jvswise/DMXW/Documentation/DMX Wireless Network Documents/Diagrams/Screenshots/Screenshot--dev-ttyUSB0 - PuTTY-2.png

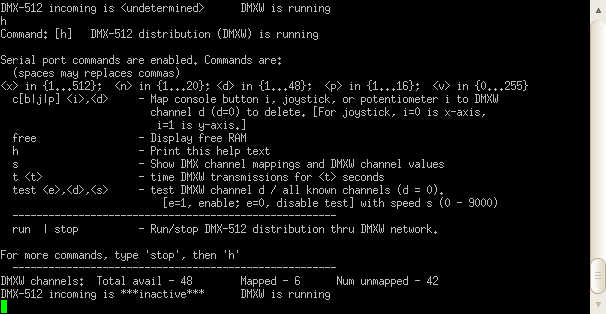
Documentation/DMX Wireless Network Documents/Diagrams/Screenshots/Screenshot--dev-ttyUSB0 - PuTTY-2.png
