jvswise/DMXW/Documentation/DMX Wireless Network Documents/Diagrams/Screenshots/Screenshot--dev-ttyUSB0 - PuTTY-3.png

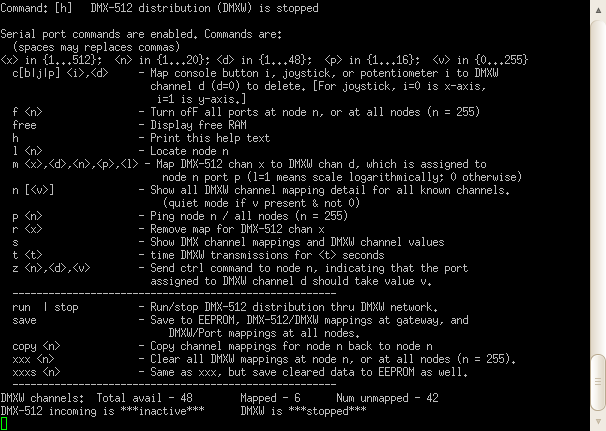
Documentation/DMX Wireless Network Documents/Diagrams/Screenshots/Screenshot--dev-ttyUSB0 - PuTTY-3.png
