jvswise/DMXW/Documentation/DMX Wireless Network Documents/Diagrams/Source Diagrams.bmp

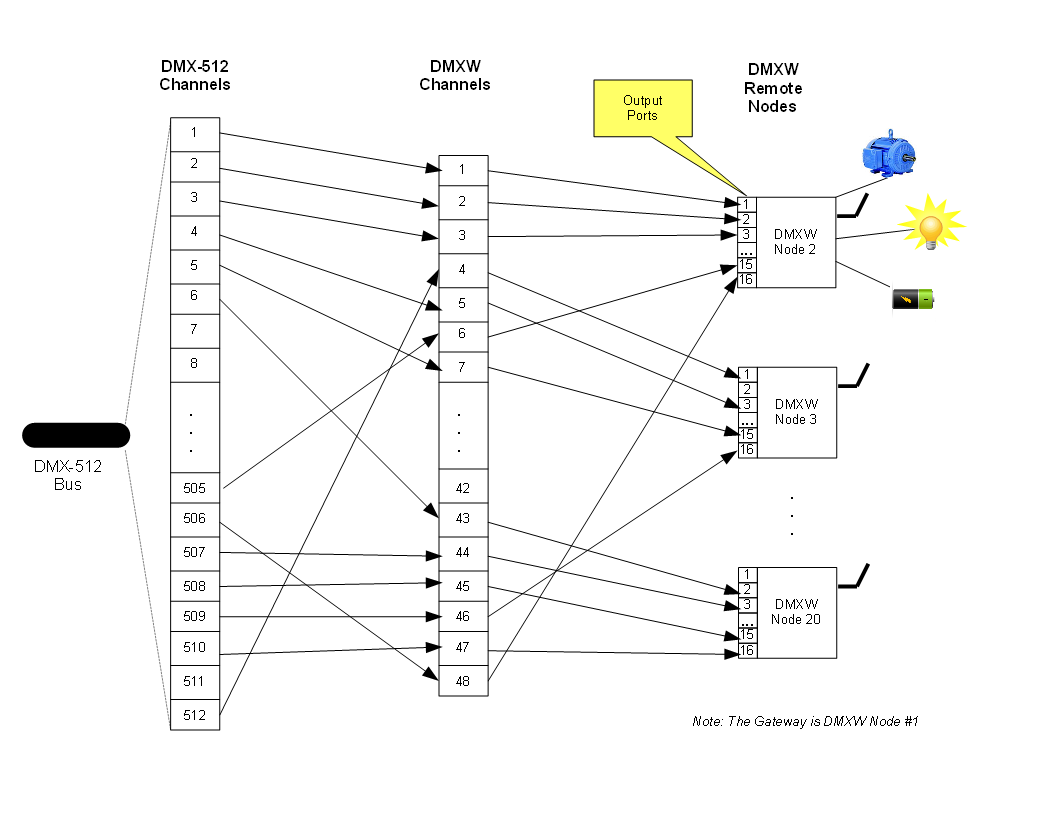
Documentation/DMX Wireless Network Documents/Diagrams/Source Diagrams.bmp
