jvswise/DMXW/Documentation/DMX Wireless Network Documents/FX modules info/Micro Fogger/DMXW micro fogger 2.jpg

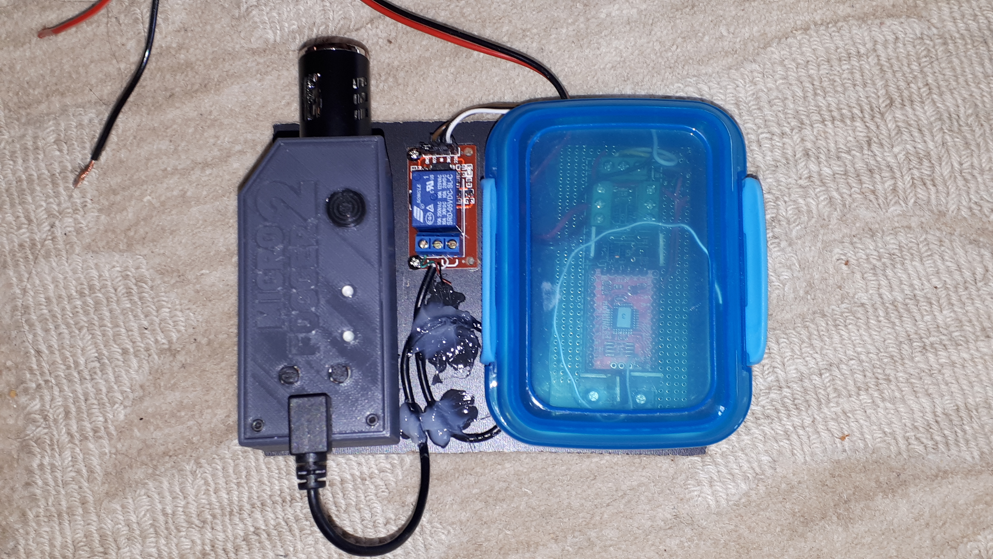
Documentation/DMX Wireless Network Documents/FX modules info/Micro Fogger/DMXW micro fogger 2.jpg
