jvswise/DMXW/Documentation/DMXW Tester Documents/DMXW Tester design notes.jpg

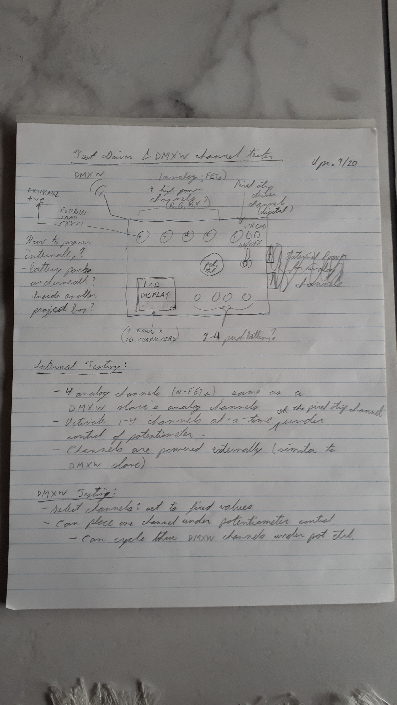
Documentation/DMXW Tester Documents/DMXW Tester design notes.jpg
