jvswise/DMXW/Documentation/DMXW Tester Documents/Photos/Channel 5 connections.jpg

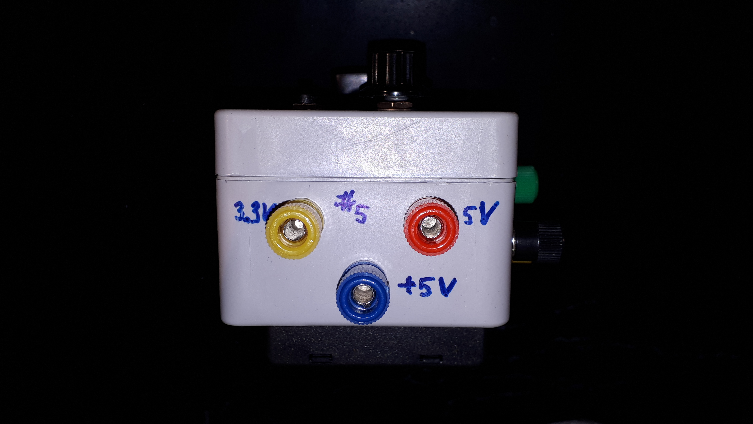
Documentation/DMXW Tester Documents/Photos/Channel 5 connections.jpg
