jvswise/DMXW/Documentation/DMXW Tester Documents/Photos/Display - Channels.jpg

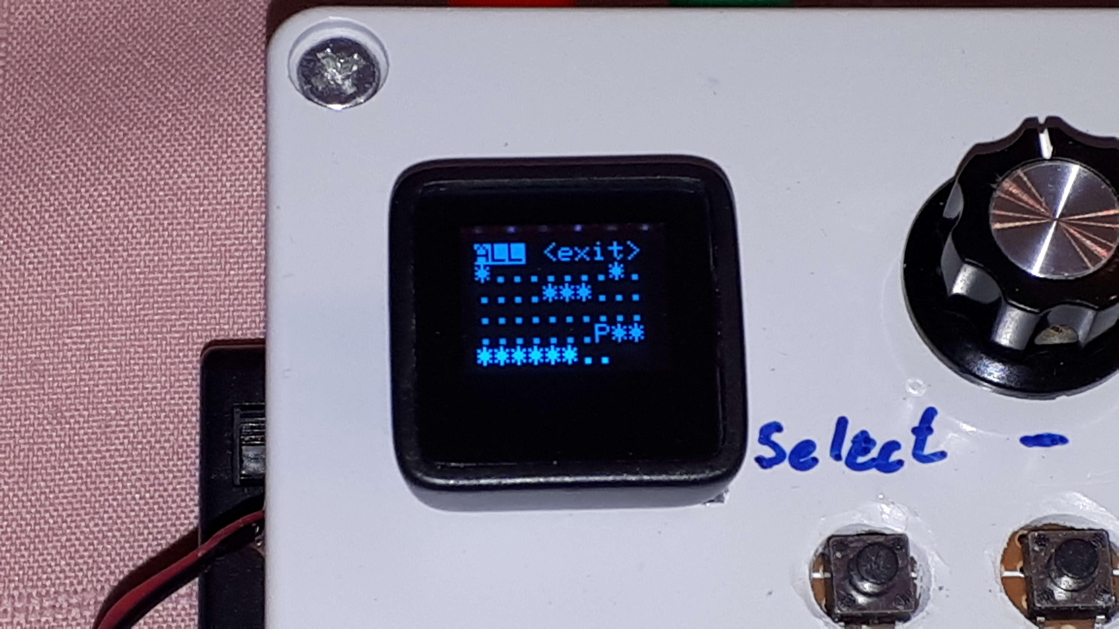
Documentation/DMXW Tester Documents/Photos/Display - Channels.jpg
