jvswise/DMXW/Documentation/DMXW Tester Documents/Photos/Display - params saved.jpg

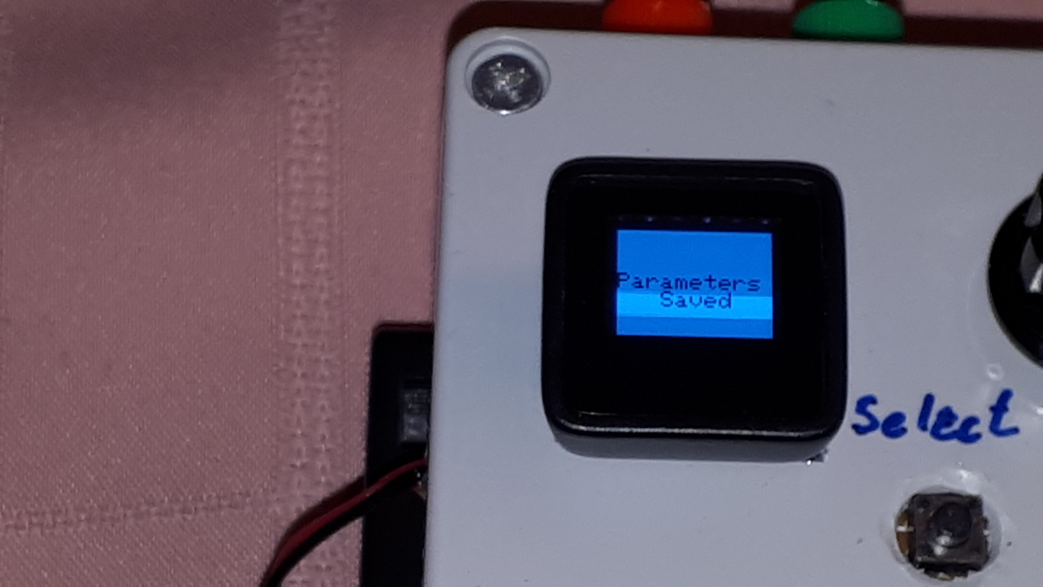
Documentation/DMXW Tester Documents/Photos/Display - params saved.jpg
