jvswise/DMXW/Documentation/DMXW Tester Documents/Photos/Display - test state.jpg

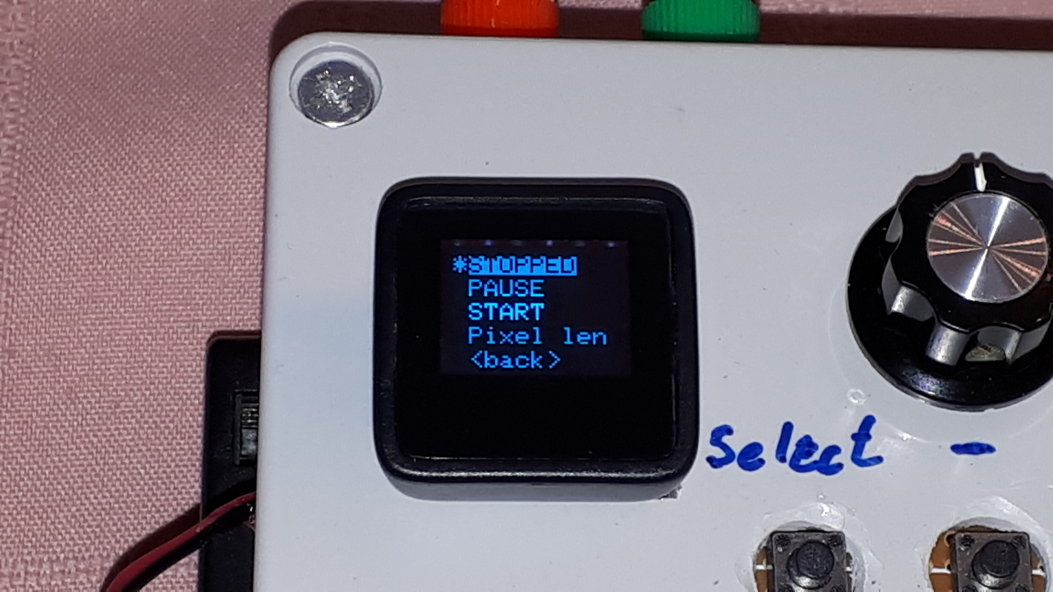
Documentation/DMXW Tester Documents/Photos/Display - test state.jpg
