jvswise/DMXW/Documentation/DMXW Tester Documents/Photos/Display - top level menu.jpg

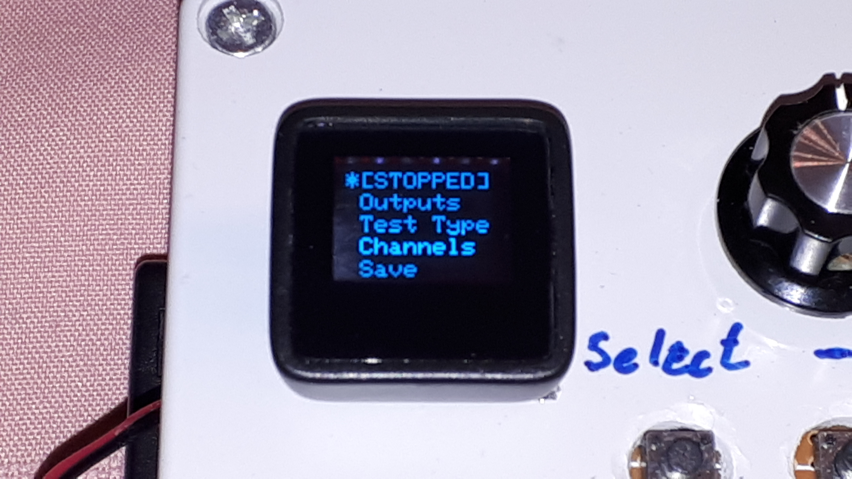
Documentation/DMXW Tester Documents/Photos/Display - top level menu.jpg
