jvswise/DMXW/Documentation/DMXW Tester Documents/Photos/Display - Values... .jpg

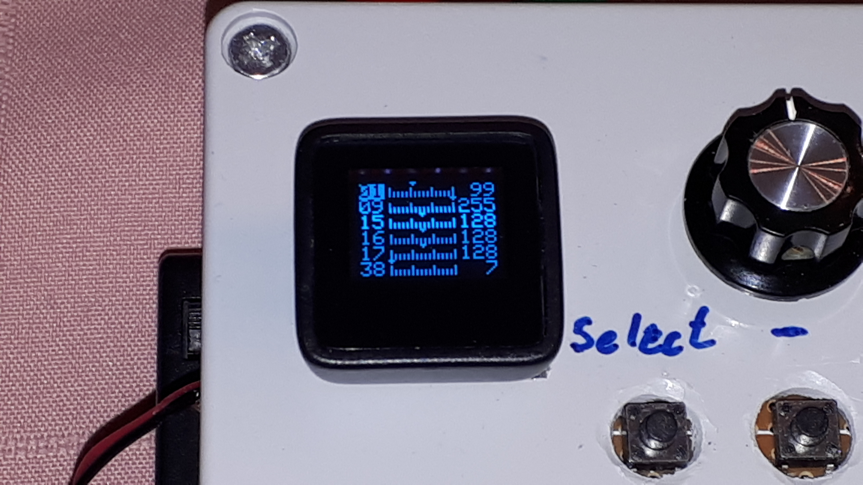
Documentation/DMXW Tester Documents/Photos/Display - Values... .jpg
