jvswise/DMXW/Documentation/DMXW Tester Documents/Photos/Top panel (battery pack underneath).jpg

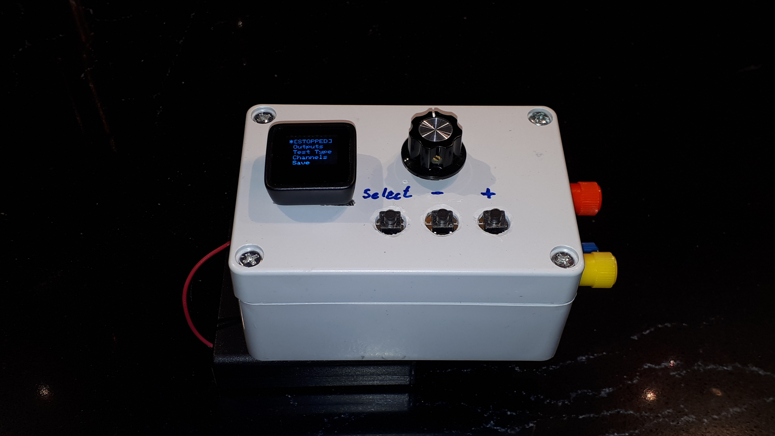
Documentation/DMXW Tester Documents/Photos/Top panel (battery pack underneath).jpg
