jvswise/DMXW/Documentation/DMX Wireless Network Documents/DMXW Node Designs/DMXW Remote Node v1.2/DMXW_Driver_Board (PCB actual size).pdf

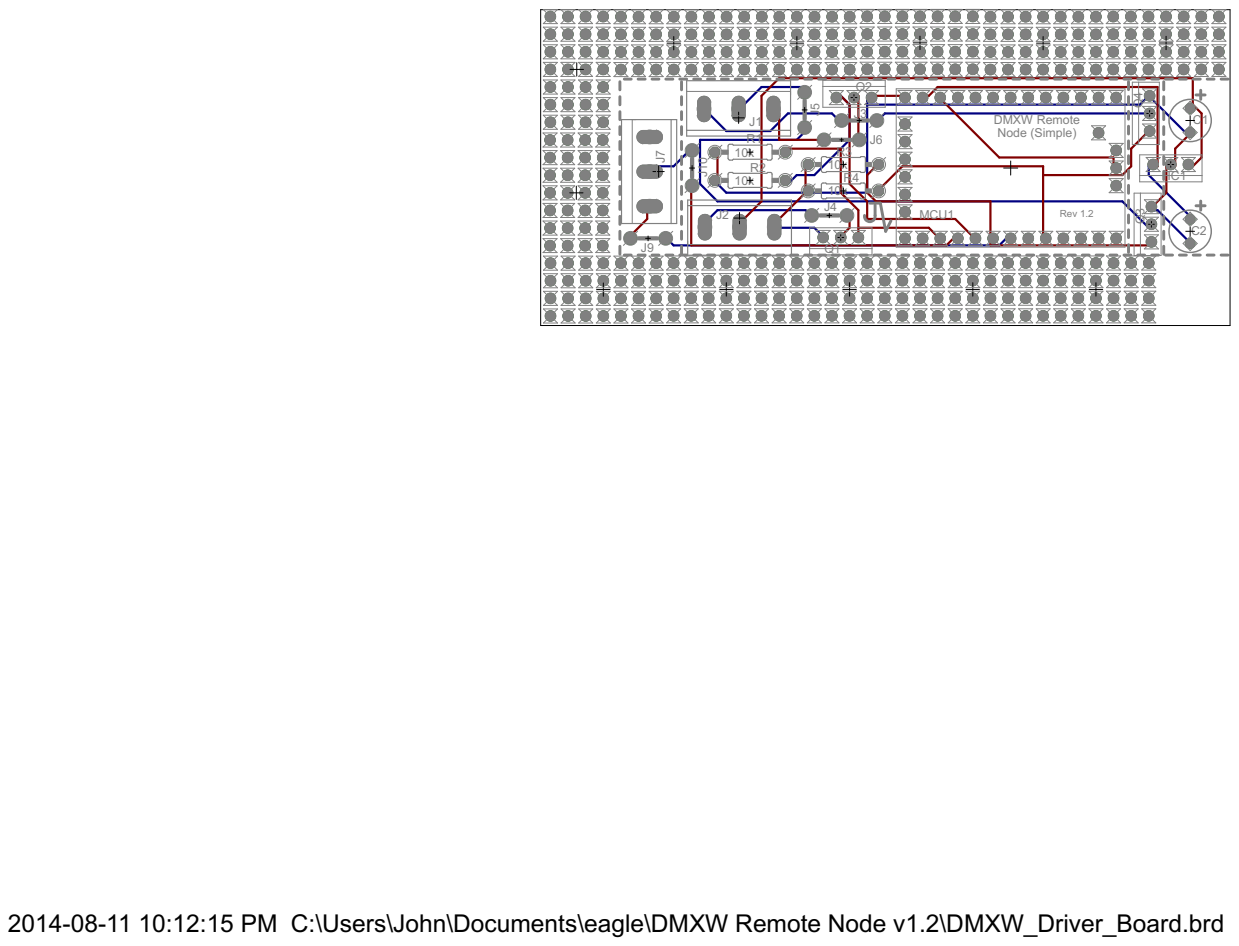
[picture p37: page 1]

2014-08-11 10:12:15 PM C:\Users\John\Documents\eagle\DMXW Remote Node v1.2\DMXW_Driver_Board.brd
