jvswise/DMXW/Documentation/DMX Wireless Network Documents/DMXW Node Designs/DMXW Remote Node v1.2/DMXW_Driver_Board.pdf

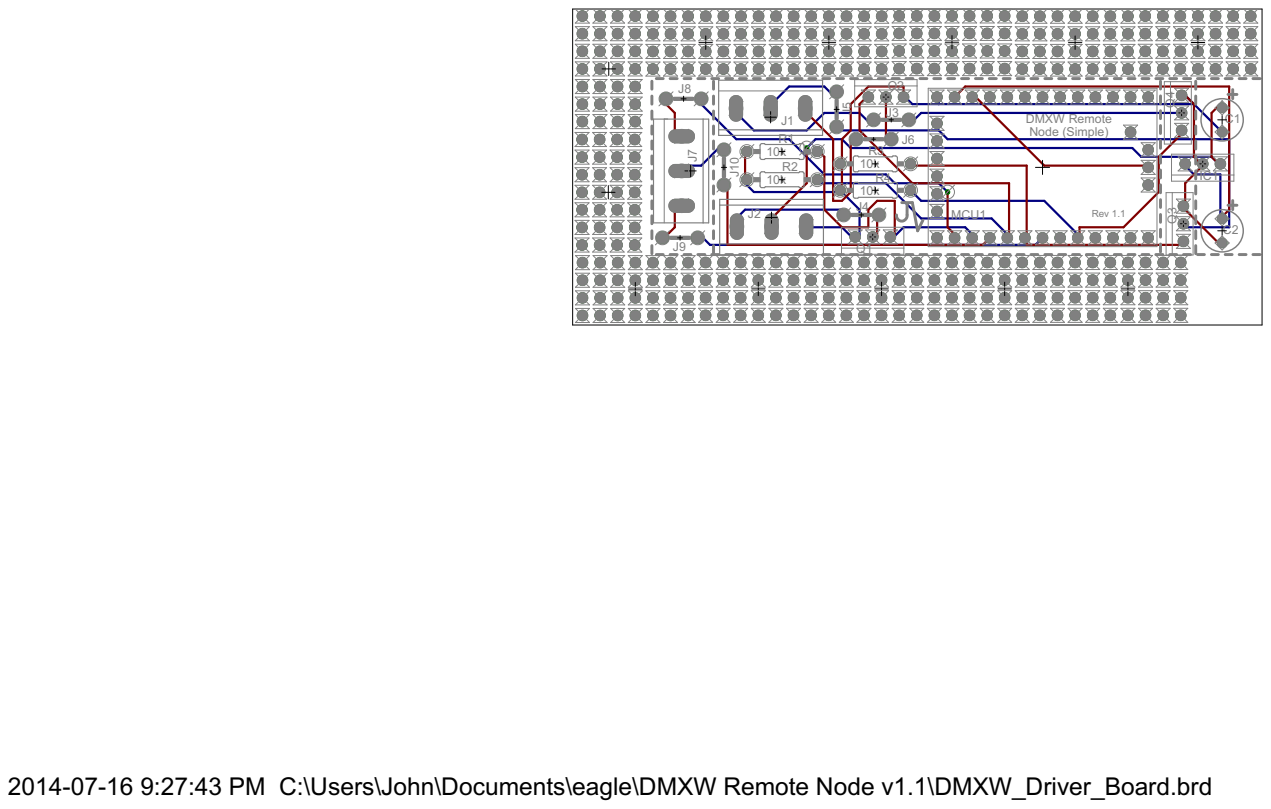
[picture p38: page 1]

2014-07-16 9:27:43 PM C:\Users\John\Documents\eagle\DMXW Remote Node v1.1\DMXW_Driver_Board.brd
